mrojas36/Coco3AppleRGB/Docs/Monitor.JPG

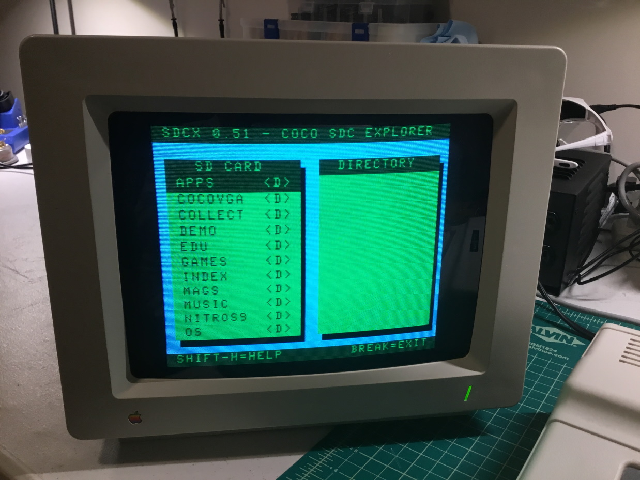
Docs/Monitor.JPG
